vr6syncro/Bambulab_Esp32_LEDController/3D Files/Render/NodeMCU.png

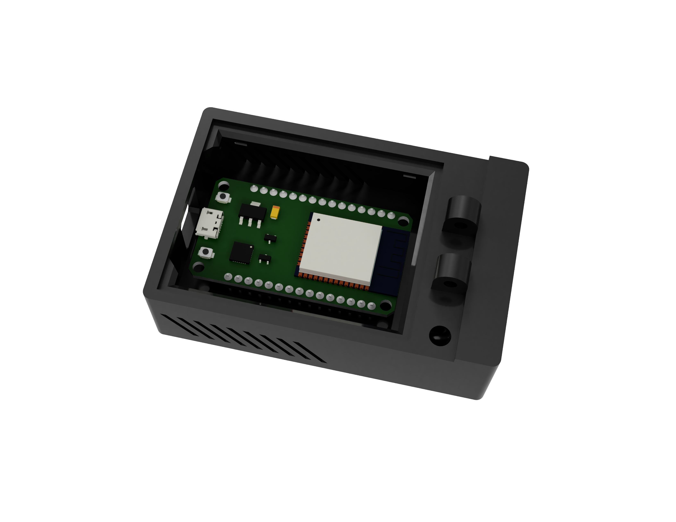
3D Files/Render/NodeMCU.png
