vr6syncro/Bambulab_Esp32_LEDController/wiki/ConsoleOutput.png

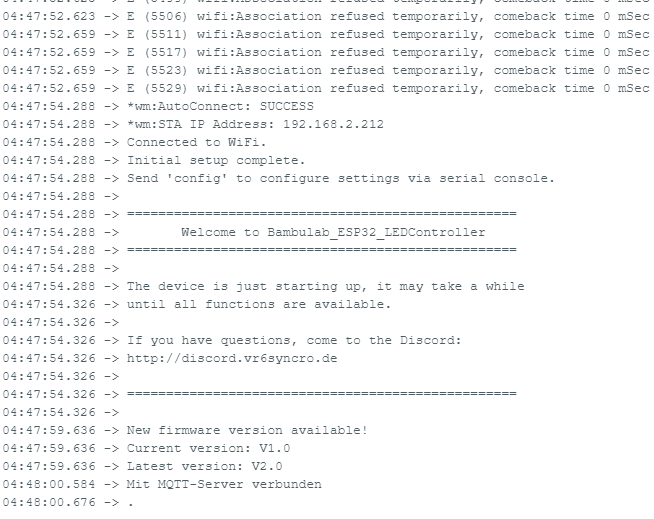
wiki/ConsoleOutput.png
