vr6syncro/Bambulab_Esp32_LEDController/wiki/InfoPage.png

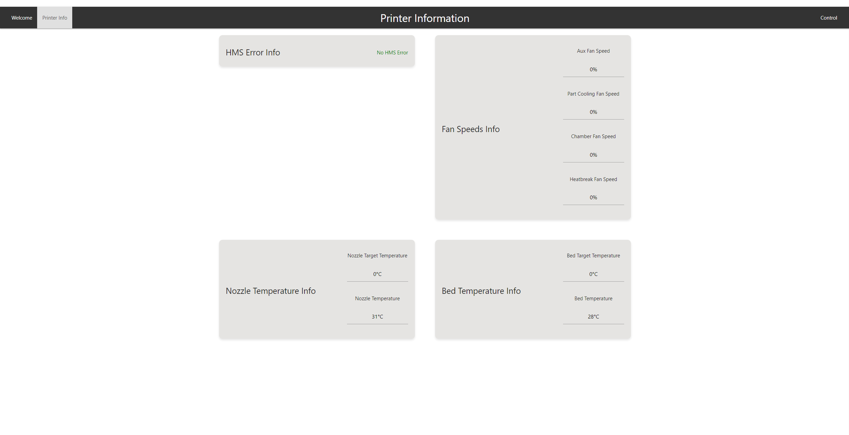
wiki/InfoPage.png
