vr6syncro/Bambulab_Esp32_LEDController/wiki/WelcomePage.png

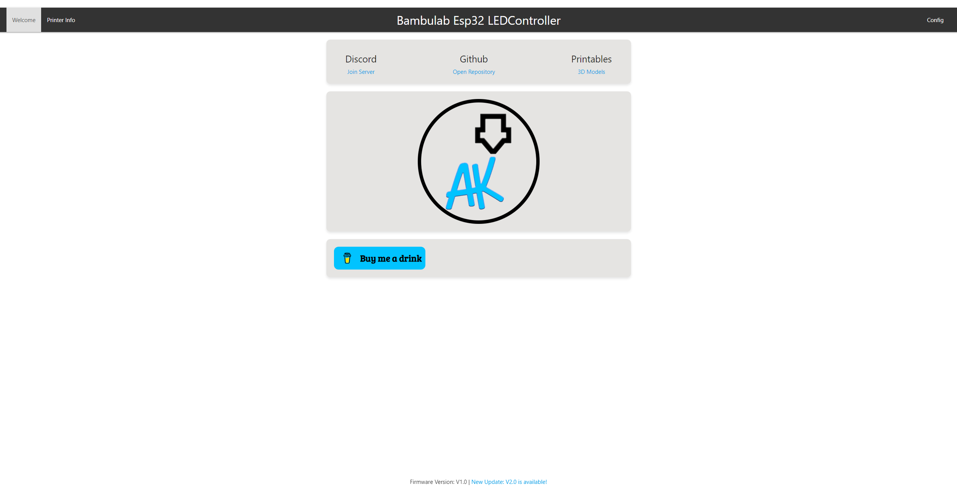
wiki/WelcomePage.png
