vr6syncro/Bambulab_Esp32_LEDController/wiki/PrinterInformation.png

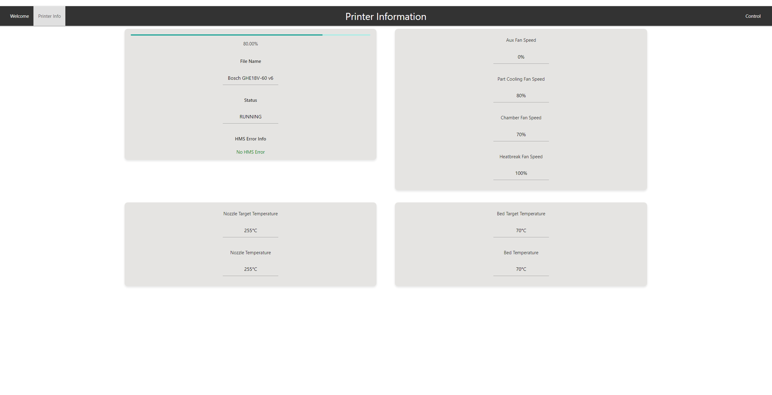
wiki/PrinterInformation.png
